Sharki-66/womo-home-esp32/firmware/sensorboard/spiffs/Ducato-grau.png

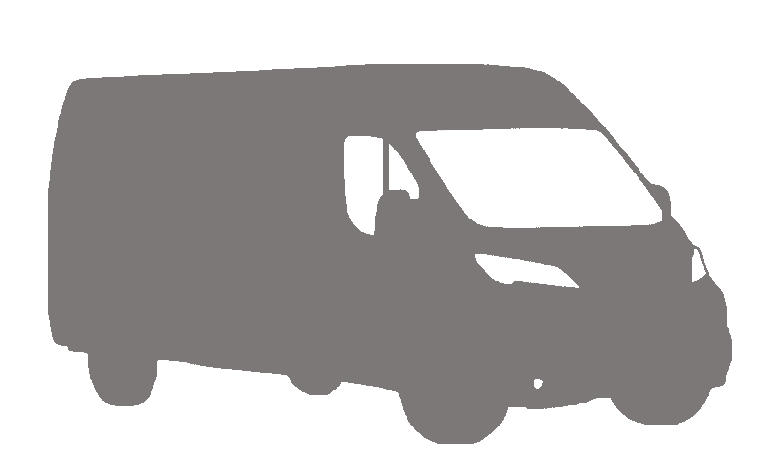
firmware/sensorboard/spiffs/Ducato-grau.png
