Sharki-66/womo-home-esp32/firmware/sensorboard/spiffs/Ducato-weiss.png

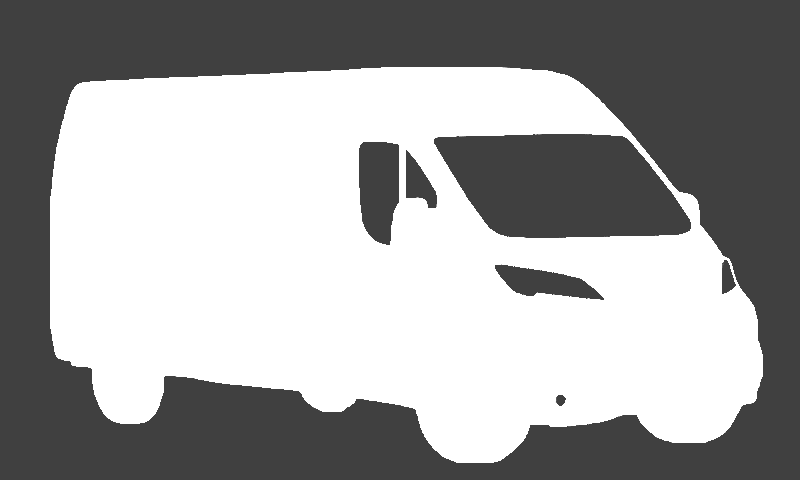
firmware/sensorboard/spiffs/Ducato-weiss.png
