Sharki-66/womo-home-esp32/hardware/datasheets/ESP32-S3-LCD-7-02.png

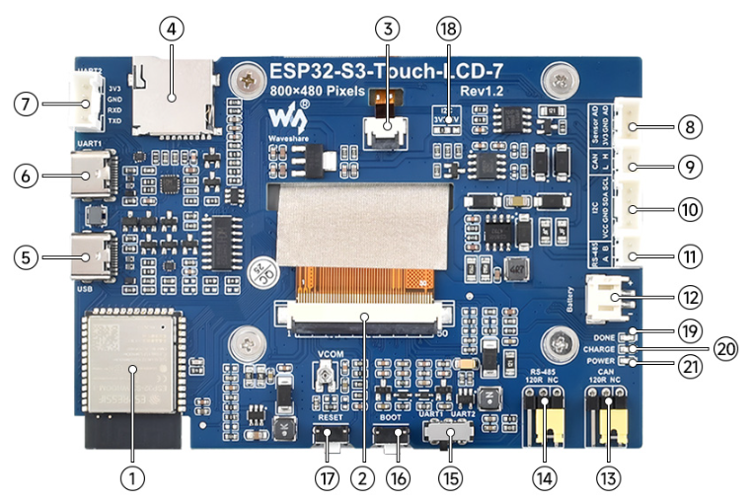
hardware/datasheets/ESP32-S3-LCD-7-02.png
