Sharki-66/womo-home-esp32/sdcard/images/ducato/Ducato.jpg

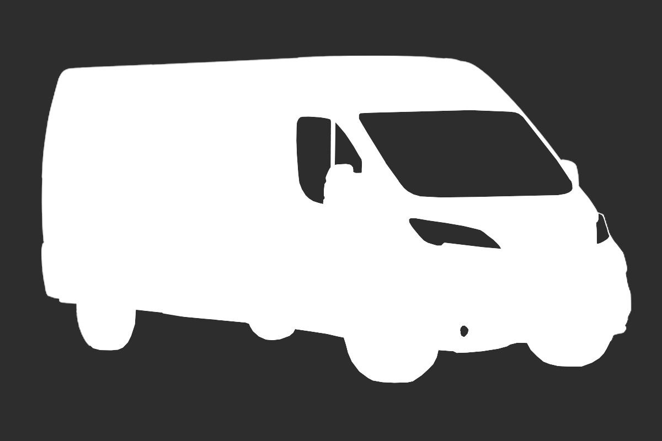
sdcard/images/ducato/Ducato.jpg
