Sharki-66/womo-home-esp32/firmware/sensorboard/components/bme680/README.md

# Bosch BME680 Sensor


License: MIT



[![Build with PlatformIO](https://img.shields.io/badge/build%20with-PlatformIO-orange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)](https://platformio.org/)



This ESP32 espressif IoT development framework (esp-idf) i2c peripheral driver was developed for the Bosch BME680 pressure, temperature, humidity and gas sensor.  Information on features and functionality are documented and can be found in the `bme680.h` header file and in the `documentation` folder.

## Repository

The component is hosted on github and is located here: <https://github.com/K0I05/ESP32-S3_ESP-IDF_COMPONENTS/tree/main/components/peripherals/i2c/esp_bme680>

## General Usage

To get started, simply copy the component to your project's `components` folder and reference the `bme680.h` header file as an include.  The component includes documentation for the peripheral such as the datasheet, application notes, and/or user manual where applicable.  There are 3 power modes supported by the BME680.  Unfortunately, 2 of three power modes (i.e. SEQUENTIAL and PARRALLEL) are not documented by Bosch and not fully implemented since these modes are not fully understood operationally.  However, the component does support multiple heater profiles through the `bme680_get_data_by_heater_profile` function.

```text
components
└── esp_bme680
    ├── CMakeLists.txt
    ├── README.md
    ├── LICENSE
    ├── idf_component.yml
    ├── library.json
    ├── documentation
    │   └── datasheets, etc.
    ├── include
    │   └── bme680_version.h
    │   └── bme680.h
    └── bme680.c
```

## Basic Example

Once a driver instance is instantiated the sensor is ready for usage as shown in the below example.   This basic implementation of the driver utilizes default configuration settings and makes a measurement request from the sensor at user defined interval and prints the results.

```c
#include <bme680.h>

void i2c0_bme680_task( void *pvParameters ) {
    // initialize the xLastWakeTime variable with the current time.
    TickType_t          last_wake_time  = xTaskGetTickCount ();
    //
    // initialize i2c device configuration
    bme680_config_t dev_cfg         = I2C_BME680_CONFIG_DEFAULT;
    bme680_handle_t dev_hdl;
    //
    // init device
    bme680_init(i2c0_bus_hdl, &dev_cfg, &dev_hdl);
    if (dev_hdl == NULL) {
        ESP_LOGE(APP_TAG, "bme680 handle init failed");
        assert(dev_hdl);
    }
    
    print_registers(dev_hdl);

    // task loop entry point
    for ( ;; ) {
        ESP_LOGI(APP_TAG, "######################## BME680 - START #########################");
        //
        // handle sensor

        bme680_data_t data;
        esp_err_t result = bme680_get_data(dev_hdl, &data);
        if(result != ESP_OK) {
            ESP_LOGE(APP_TAG, "bme680 device read failed (%s)", esp_err_to_name(result));
        } else {
            data.barometric_pressure = data.barometric_pressure / 100;
            ESP_LOGI(APP_TAG, "air temperature:     %.2f °C", data.air_temperature);
            ESP_LOGI(APP_TAG, "dewpoint temperature:%.2f °C", data.dewpoint_temperature);
            ESP_LOGI(APP_TAG, "relative humidity:   %.2f %%", data.relative_humidity);
            ESP_LOGI(APP_TAG, "barometric pressure: %.2f hPa", data.barometric_pressure);
            ESP_LOGI(APP_TAG, "gas resistance:      %.2f kOhms", data.gas_resistance/1000);
            ESP_LOGI(APP_TAG, "iaq score:           %u (%s)", data.iaq_score, bme680_iaq_air_quality_to_string(data.iaq_score));
        }
        //
        ESP_LOGI(APP_TAG, "######################## BME680 - END ###########################");
        //
        //
        // pause the task per defined wait period
        vTaskDelaySecUntil( &last_wake_time, I2C0_TASK_SAMPLING_RATE );
    }
    //
    // free resources
    bme680_delete( dev_hdl );
    vTaskDelete( NULL );
}
```

Copyright (c) 2025 Eric Gionet (<gionet.c.eric@gmail.com>)
