Sharki-66/womo-home-esp32/firmware/sensorboard/main/network/wifi/sensor_wifi.h

/*
 * SPDX-FileCopyrightText: 2025-2026 Hajo Harms
 *
 * SPDX-License-Identifier: MIT
 */

#pragma once

#include "esp_err.h"
#include <stdbool.h>
#include <stddef.h>

#ifdef __cplusplus
extern "C" {
#endif

/**
 * WiFi STA-Modul für das Sensorboard.
 *
 * Verbindet sich als Station mit dem RUTX11 Router.
 * SSID/Passwort werden aus NVS gelesen (Fallback: sensor_config.h Defaults).
 * mDNS registriert den Hostnamen "womo-sensor.local".
 */

/// Initialisiert WiFi-STA (netif, event-loop, NVS-Credentials, mDNS).
/// Startet die Verbindung automatisch.
esp_err_t sensor_wifi_init(void);

/// Stoppt WiFi und gibt Ressourcen frei.
esp_err_t sensor_wifi_deinit(void);

/// Gibt true zurück wenn WiFi verbunden und IP vorhanden.
bool sensor_wifi_is_connected(void);

/// WiFi-Credentials im NVS aktualisieren und neu verbinden.
/// ssid/pass dürfen NULL sein (dann wird der jeweilige Wert nicht geändert).
esp_err_t sensor_wifi_set_credentials(const char *ssid, const char *pass);

/// Callback-Typ: wird aufgerufen wenn WiFi nach max. Retries nicht verbinden kann.
/// Nutzbar z.B. um per ESP-NOW das Passwort beim Display anzufragen.
typedef void (*sensor_wifi_auth_fail_cb_t)(void);

/// Registriert den Auth-Failure-Callback (nur einer, überschreibbar).
void sensor_wifi_set_auth_fail_cb(sensor_wifi_auth_fail_cb_t cb);

/// Liefert die aktuelle IP-Adresse als String (z.B. "192.168.1.120").
/// Gibt leeren String zurück wenn nicht verbunden.
const char *sensor_wifi_get_ip_str(void);

/// Liefert SSID und RSSI des verbundenen APs.
/// ssid_out: Buffer min. 33 Byte. rssi_out: RSSI-Wert (negativ). 
/// Gibt true zurück wenn verbunden, sonst false (Puffer werden auf 0/"" gesetzt).
bool sensor_wifi_get_ap_info(char *ssid_out, size_t ssid_len, int8_t *rssi_out);

#ifdef __cplusplus
}
#endif
