Sharki-66/womo-home-esp32/firmware/sensorboard/main/time/rtc_pcf8523.c

/*
 * SPDX-FileCopyrightText: 2025-2026 Hajo Harms
 *
 * SPDX-License-Identifier: MIT
 */

#include "time/rtc_pcf8523.h"

#include <stdio.h>
#include <time.h>
#include "freertos/FreeRTOS.h"
#include "freertos/task.h"
#include "esp_check.h"
#include "esp_log.h"
#include "driver/i2c_master.h"
#include "hal/sensor_i2c_bus.h"
#include "sensor_config.h"

// PCF8523 Control_3 Bits
#define PCF8523_CTRL3_PM2       (1 << 7)  // Power Management Bit 2
#define PCF8523_CTRL3_PM1       (1 << 6)  // Power Management Bit 1
#define PCF8523_CTRL3_PM0       (1 << 5)  // Power Management Bit 0
#define PCF8523_CTRL3_BSF       (1 << 4)  // Battery Switch-over Flag (VDD-Ausfall erkannt)
#define PCF8523_CTRL3_BLF       (1 << 3)  // Battery Low Flag (Spannung < ~1.2V)
#define PCF8523_CTRL3_BSIE      (1 << 1)  // Battery Switch-over Interrupt Enable
#define PCF8523_CTRL3_BLIE      (1 << 0)  // Battery Low Interrupt Enable

#define PCF8523_ADDR            0x68
#define PCF8523_REG_CONTROL_1   0x00
#define PCF8523_REG_CONTROL_3   0x02
#define PCF8523_REG_SECONDS     0x03

#define PCF8523_LOG_INTERVAL_MS 5000

static const char *TAG = "pcf8523_app";

static i2c_master_dev_handle_t s_dev = NULL;
static TaskHandle_t s_task = NULL;

static uint8_t bcd2dec(uint8_t val)
{
    return (val >> 4) * 10 + (val & 0x0F);
}

static uint8_t dec2bcd(uint8_t val)
{
    return ((val / 10) << 4) | (val % 10);
}

static bool is_leap_year(int year)
{
    if (year % 400 == 0) {
        return true;
    }
    if (year % 100 == 0) {
        return false;
    }
    return (year % 4 == 0);
}

static time_t tm_to_epoch_utc(const struct tm *tm_utc)
{
    static const int days_before_month[] = {
        0, 31, 59, 90, 120, 151, 181, 212, 243, 273, 304, 334
    };
    int year = tm_utc->tm_year + 1900;
    int month = tm_utc->tm_mon + 1;
    int day = tm_utc->tm_mday;

    int64_t days = 0;
    for (int y = 1970; y < year; y++) {
        days += is_leap_year(y) ? 366 : 365;
    }

    days += days_before_month[month - 1];
    if (month > 2 && is_leap_year(year)) {
        days += 1;
    }
    days += (day - 1);

    int64_t seconds = (days * 86400LL)
                      + (tm_utc->tm_hour * 3600LL)
                      + (tm_utc->tm_min * 60LL)
                      + tm_utc->tm_sec;
    return (time_t)seconds;
}

static esp_err_t pcf8523_read(uint8_t reg, uint8_t *buf, size_t len)
{
    i2c_bus_lock();
    esp_err_t err = i2c_master_transmit_receive(s_dev, &reg, 1, buf, len, 500);
    i2c_bus_unlock();
    return err;
}

static esp_err_t pcf8523_write_byte(uint8_t reg, uint8_t value)
{
    uint8_t data[2] = {reg, value};
    i2c_bus_lock();
    esp_err_t err = i2c_master_transmit(s_dev, data, sizeof(data), 500);
    i2c_bus_unlock();
    return err;
}

static esp_err_t pcf8523_write_regs(uint8_t start_reg, const uint8_t *data, size_t len)
{
    uint8_t buf[1 + 8] = {0};
    if (len > 8) {
        return ESP_ERR_INVALID_ARG;
    }
    buf[0] = start_reg;
    for (size_t i = 0; i < len; i++) {
        buf[1 + i] = data[i];
    }
    i2c_bus_lock();
    esp_err_t err = i2c_master_transmit(s_dev, buf, 1 + len, 500);
    i2c_bus_unlock();
    return err;
}

static esp_err_t pcf8523_set_24h_mode(void)
{
    uint8_t ctrl = 0;
    esp_err_t err = pcf8523_read(PCF8523_REG_CONTROL_1, &ctrl, 1);
    if (err != ESP_OK) {
        return err;
    }
    ctrl &= ~(1 << 3); // 12/24h = 0 -> 24h
    return pcf8523_write_byte(PCF8523_REG_CONTROL_1, ctrl);
}

static void pcf8523_task(void *arg)
{
    const TickType_t delay_ticks = pdMS_TO_TICKS(PCF8523_LOG_INTERVAL_MS);
    while (1) {
        uint8_t buf[7] = {0};
        esp_err_t err = pcf8523_read(PCF8523_REG_SECONDS, buf, sizeof(buf));
        if (err == ESP_OK) {
            bool os_flag = (buf[0] & 0x80) != 0; // Oscillator Stop Flag
            int sec = bcd2dec(buf[0] & 0x7F);
            int min = bcd2dec(buf[1] & 0x7F);
            int hour = bcd2dec(buf[2] & 0x3F);
            int day = bcd2dec(buf[3] & 0x3F);
            int month = bcd2dec(buf[5] & 0x1F);
            int year = bcd2dec(buf[6]) + 2000;
            if (os_flag) {
                ESP_LOGW(TAG, "RTC: OS-Flag gesetzt – Zeit ungültig (noch nie gesetzt)");
            } else {
                ESP_LOGI(TAG, "RTC: %04d-%02d-%02d %02d:%02d:%02d",
                         year, month, day, hour, min, sec);
            }
        } else {
            ESP_LOGW(TAG, "RTC lesen fehlgeschlagen (%s)", esp_err_to_name(err));
        }
        vTaskDelay(delay_ticks);
    }
}
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
